ajisaacs/OpenNest/screenshots/screenshot-cad-converter-1.png

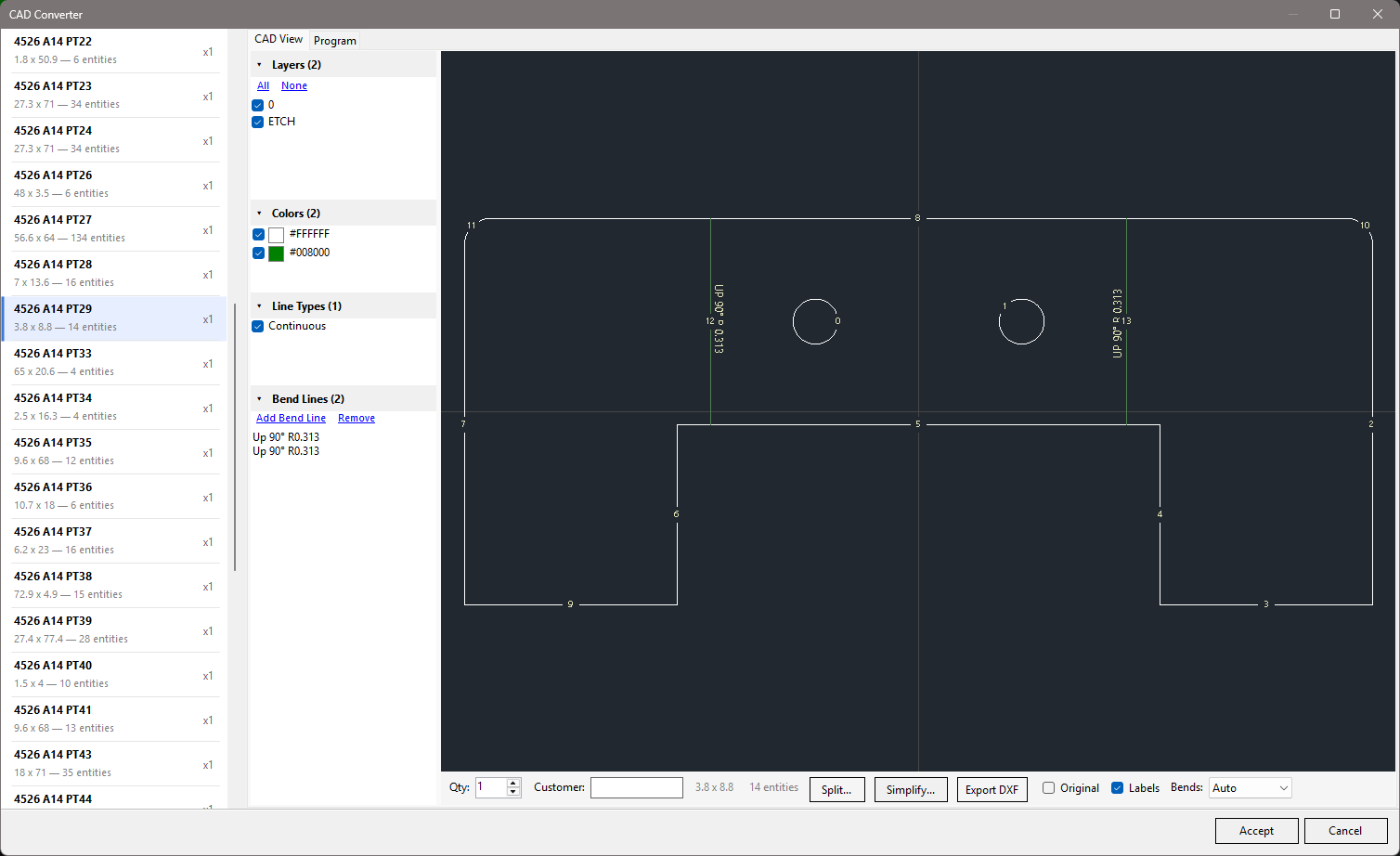
screenshots/screenshot-cad-converter-1.png
