ajisaacs/OpenNest/screenshots/screenshot-cad-converter-2.png

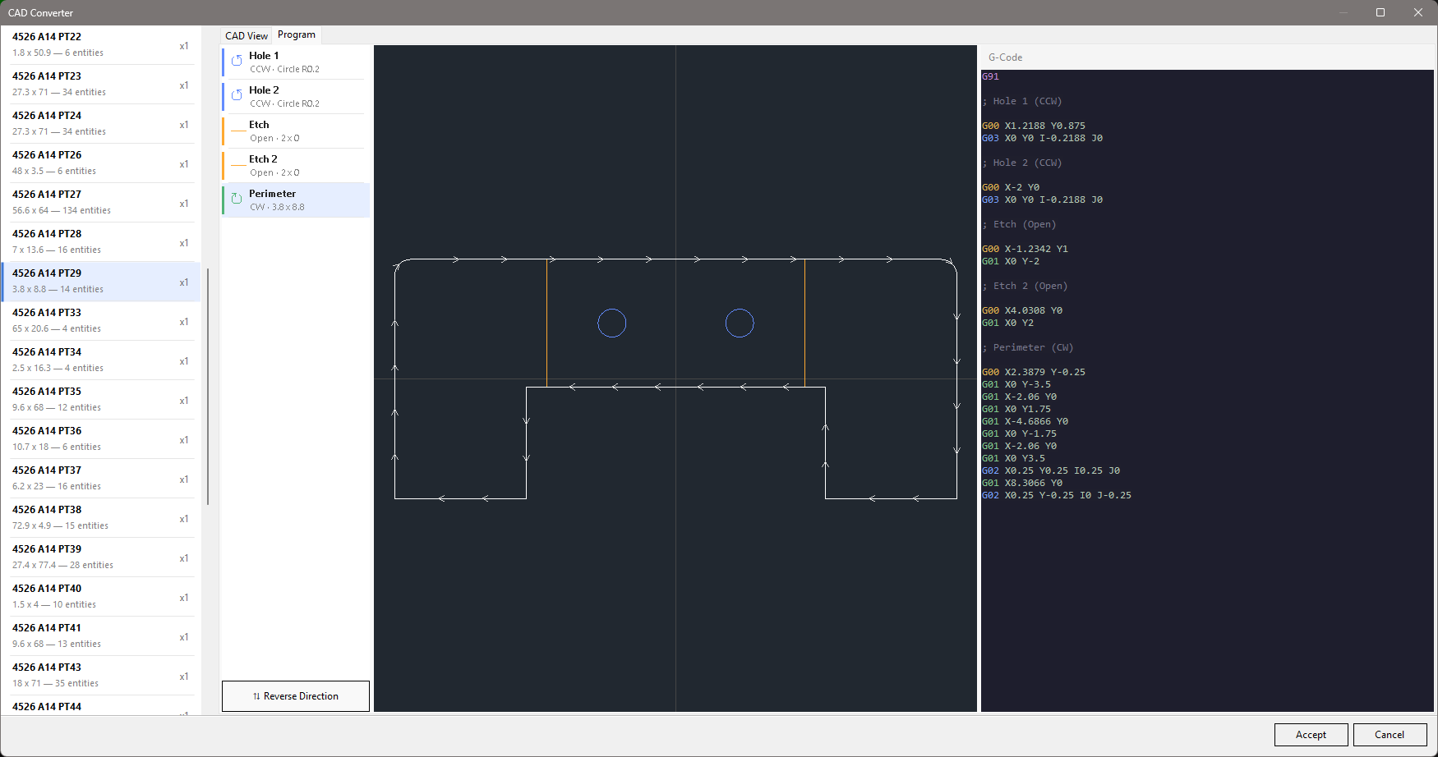
screenshots/screenshot-cad-converter-2.png
